DJdaGOAT1/CrickHit/src/Sound.h

// Sound.h
// Runs on MSPM0
// Play sounds on 5-bit DAC.
// Your name
// 11/5/2023
#ifndef SOUND_H
#define SOUND_H
#include <stdint.h>

// initialize a 11kHz SysTick, however no sound should be started
// initialize any global variables
// Initialize the 5 bit DAC
// This is called once
void Sound_Init(void);

//******* Sound_Start ************
// This function does not output to the DAC. 
// Rather, it sets a pointer and counter, and then enables the SysTick interrupt.
// It starts the sound, and the SysTick ISR does the output
// feel free to change the parameters
// Sound should play once and stop
// Input: pt is a pointer to an array of DAC outputs
//        count is the length of the array
// Output: none
// special cases: as you wish to implement
void Sound_Start(const uint8_t *pt, uint32_t count);

// Play the bat-hit sound once (triggered every time the batsman hits the ball)
void Sound_BatHit(void);


// Play the stump-hit sound once (triggered when the ball hits the stumps)
void Sound_StumpHit(void);

// Play the IPL stadium crowd once at system start; never loops
void Sound_IPLStadium(void);

void Speaker_Enable();
void Speaker_Disable();
void Speaker_Toggle();

// following 8 functions do not output to the DAC
// they configure pointers/counters and initiate the sound by calling Sound_Start
void Sound_Shoot(void);
void Sound_Killed(void);
void Sound_Explosion(void);
void Sound_Fastinvader1(void);
void Sound_Fastinvader2(void);
void Sound_Fastinvader3(void);
void Sound_Fastinvader4(void);
void Sound_Highpitch(void);

#endif
